bardolf/fatrug2/src/detector.h

#ifndef detector_h
#define detector_h

#include <Arduino.h>

#define TRIGGER_PIN 26
#define ECHO_PIN 25
#define RANGE_THRESHOLD_CM 70
#define SOUND_SPEED_HALF 0.017
#define DISTANCE_RELATIVE_TOLERANCE 0.2

typedef enum {
    NONE,
    ARRIVED,
    LEFT
} DetectedObjectState;

class Detector {
   public:
    Detector();
    void init();
    DetectedObjectState read();
    void startMeasurement();
    void stopMeasurement();
    uint32_t getCompensationTime();

   private:
    bool _prevObjectDetected;
    bool _measurementEnabled = false;
    float measureDistance();
    unsigned long _detectorPulseInTimeout;

    float _distance;
    float _prevDistance;
    float _prevPrevDistance;
    
    uint32_t _time;
    uint32_t _prevTime;    
    uint32_t _prevPrevTime;
    

};

#endif
