bardolf/fatrug2/src/logging.cpp

#include "logging.h"

void printPrefix(Print* _logOutput, int logLevel) {
    printTimestamp(_logOutput);
    printLogLevel (_logOutput, logLevel);
}

void printTimestamp(Print* _logOutput) {

  // Division constants
  const unsigned long MSECS_PER_SEC       = 1000;
  const unsigned long SECS_PER_MIN        = 60;
  const unsigned long SECS_PER_HOUR       = 3600;
  const unsigned long SECS_PER_DAY        = 86400;

  // Total time
  const unsigned long msecs               =  millis() ;
  const unsigned long secs                =  msecs / MSECS_PER_SEC;

  // Time in components
  const unsigned long MiliSeconds         =  msecs % MSECS_PER_SEC;
  const unsigned long Seconds             =  secs  % SECS_PER_MIN ;
  const unsigned long Minutes             = (secs  / SECS_PER_MIN) % SECS_PER_MIN;
  const unsigned long Hours               = (secs  % SECS_PER_DAY) / SECS_PER_HOUR;

  // Time as string
  char timestamp[20];
  sprintf(timestamp, "%02d:%02d:%02d.%03d ", Hours, Minutes, Seconds, MiliSeconds);
  _logOutput->print(timestamp);
}


void printLogLevel(Print* _logOutput, int logLevel) {    
    switch (logLevel)
    {
        default:
        case 0:_logOutput->print("SILENT  "); break;
        case 1:_logOutput->print("FATAL   "); break;
        case 2:_logOutput->print("ERROR   "); break;
        case 3:_logOutput->print("WARNING "); break;
        case 4:_logOutput->print("INFO    "); break;
        case 5:_logOutput->print("TRACE   "); break;
        case 6:_logOutput->print("VERBOSE "); break;
    }   
}
